josalggui/RFAutoMaTE/figures/Block diagram.png

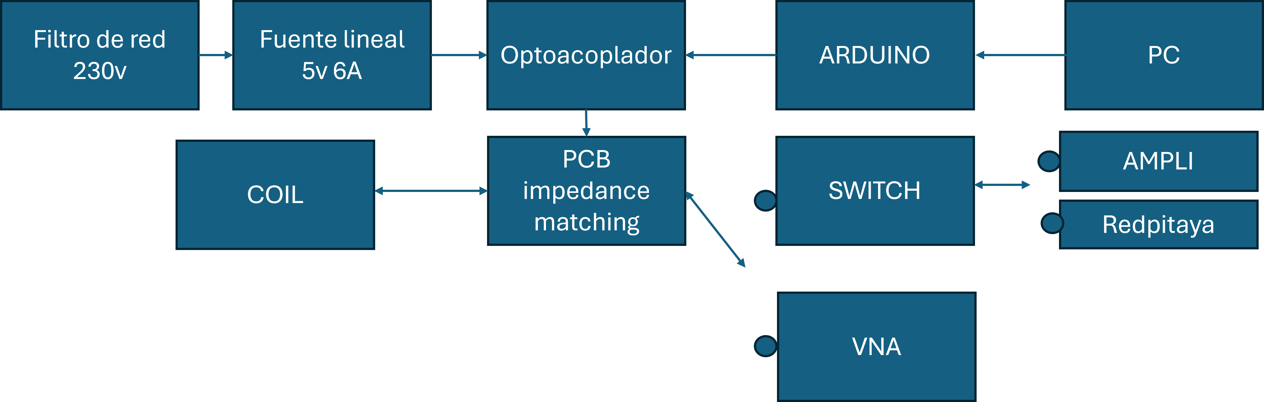
figures/Block diagram.png
