josalggui/RFAutoMaTE/figures/caja 2.jpg

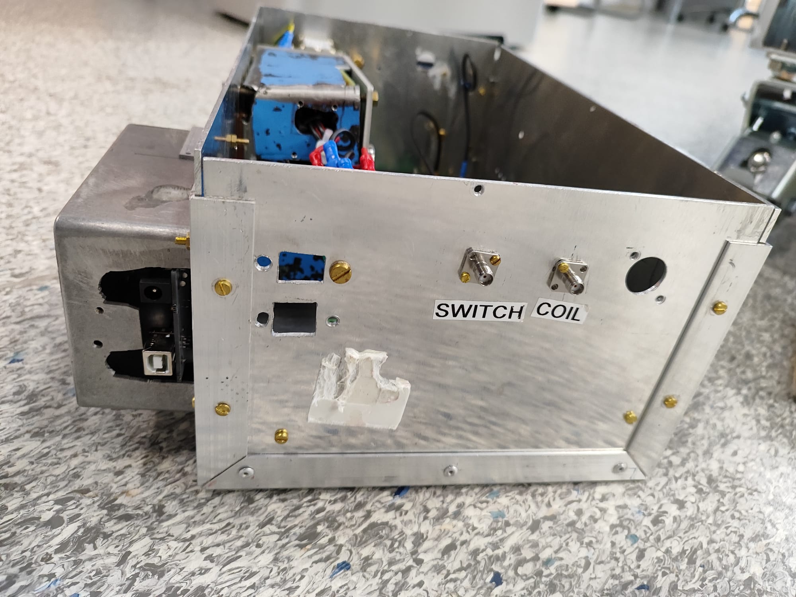
figures/caja 2.jpg
