josalggui/RFAutoMaTE/figures/caja 5.jpg

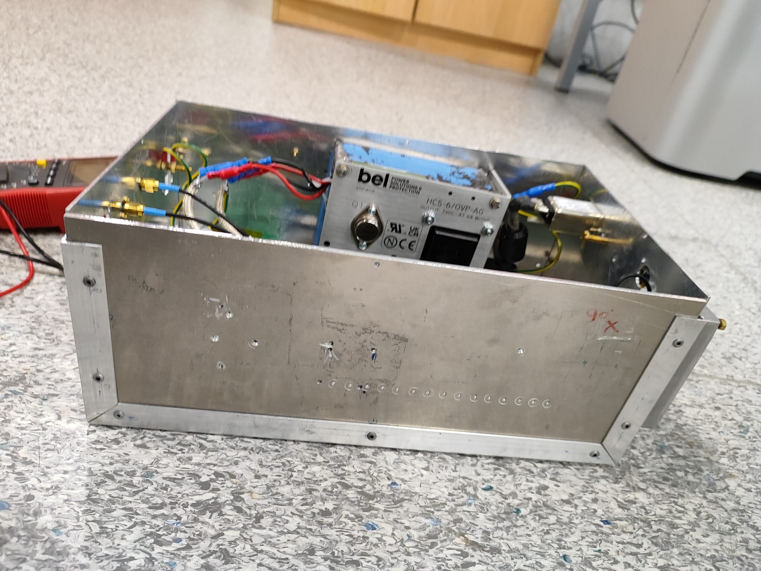
figures/caja 5.jpg
