josalggui/RFAutoMaTE/figures/caja 6.jpg

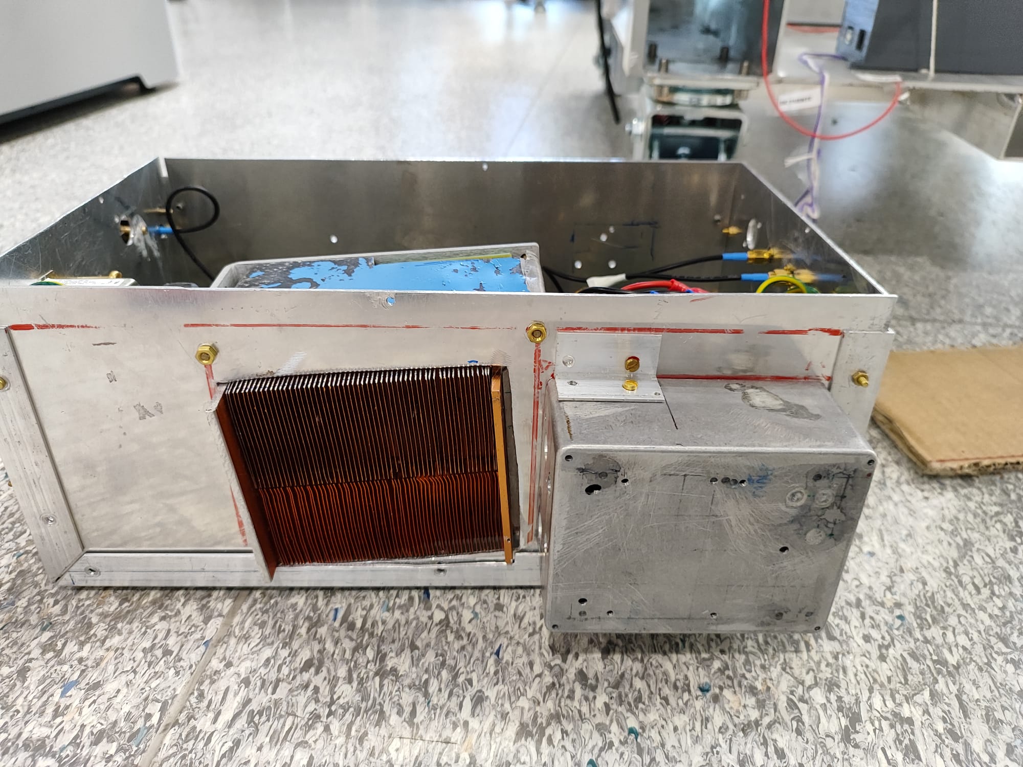
figures/caja 6.jpg
