josalggui/RFAutoMaTE/figures/fuenet lineal 2.jpg

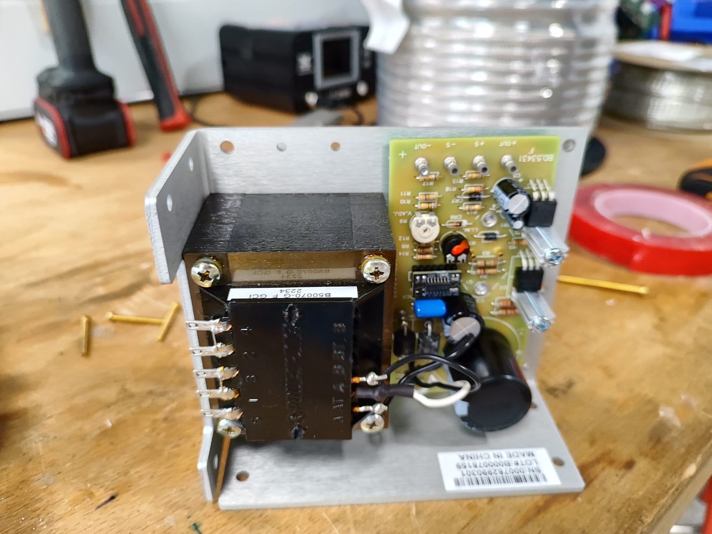
figures/fuenet lineal 2.jpg
