josalggui/RFAutoMaTE/figures/fuenet lineal 3.jpg

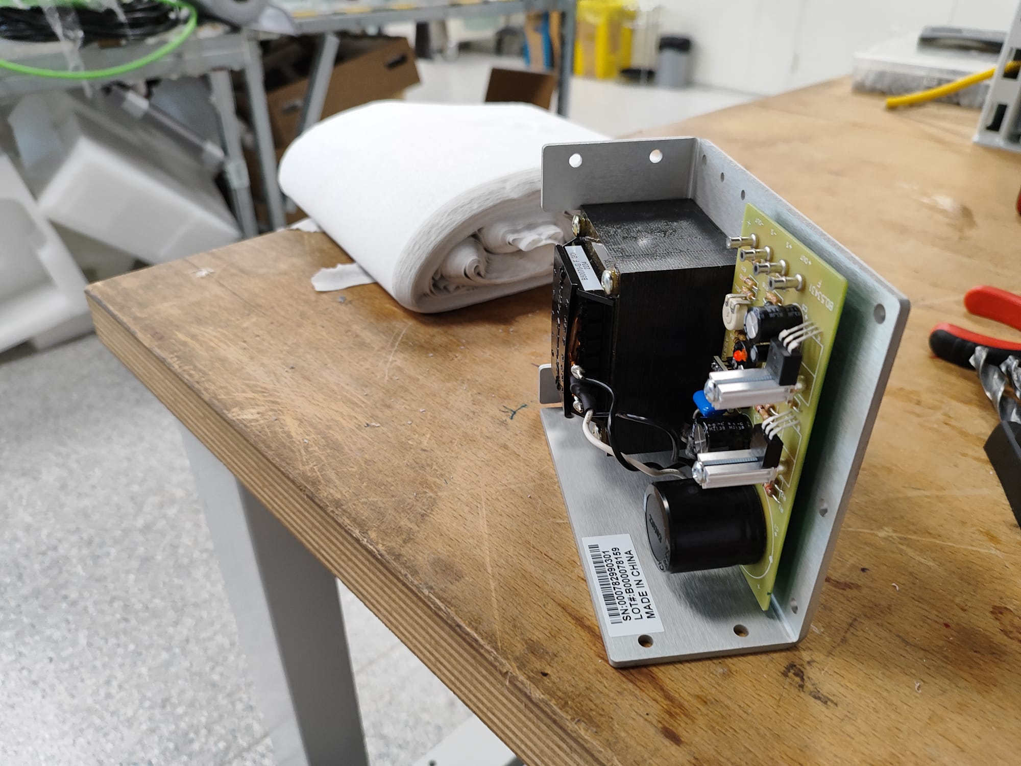
figures/fuenet lineal 3.jpg
