josalggui/RFAutoMaTE/figures/fuenete lineal 4.jpg

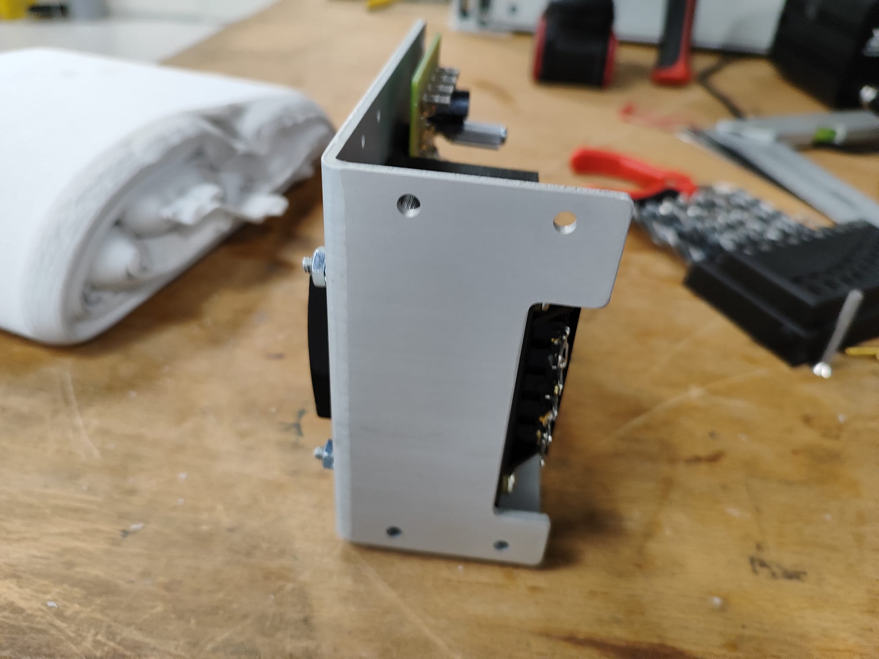
figures/fuenete lineal 4.jpg
