josalggui/RFAutoMaTE/figures/pcb sin montar2.jpg

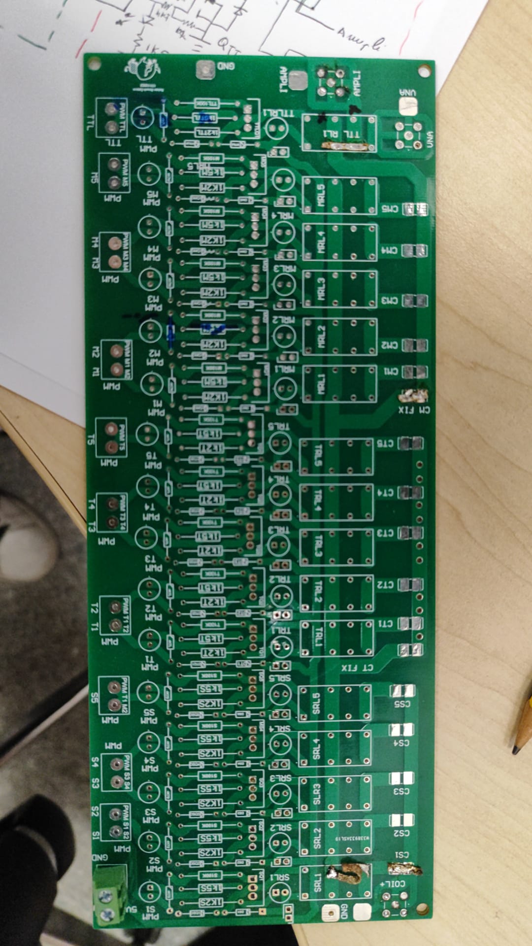
figures/pcb sin montar2.jpg
