josalggui/RFAutoMaTE/figures/pcb sin montar3.jpg

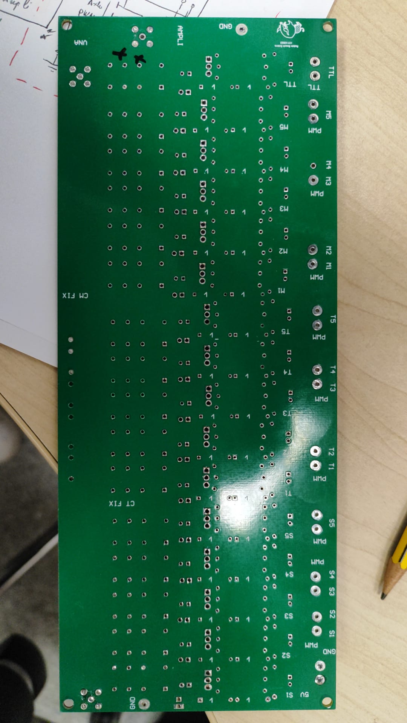
figures/pcb sin montar3.jpg
