josalggui/RFAutoMaTE/optoacoplador/NPN.PNG

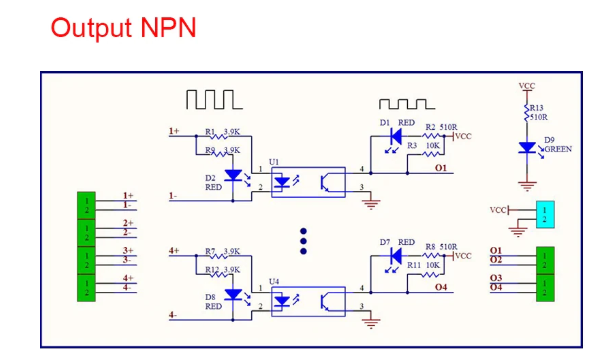
optoacoplador/NPN.PNG
