josalggui/RFAutoMaTE/PCB/Aclaración esquema.jpg

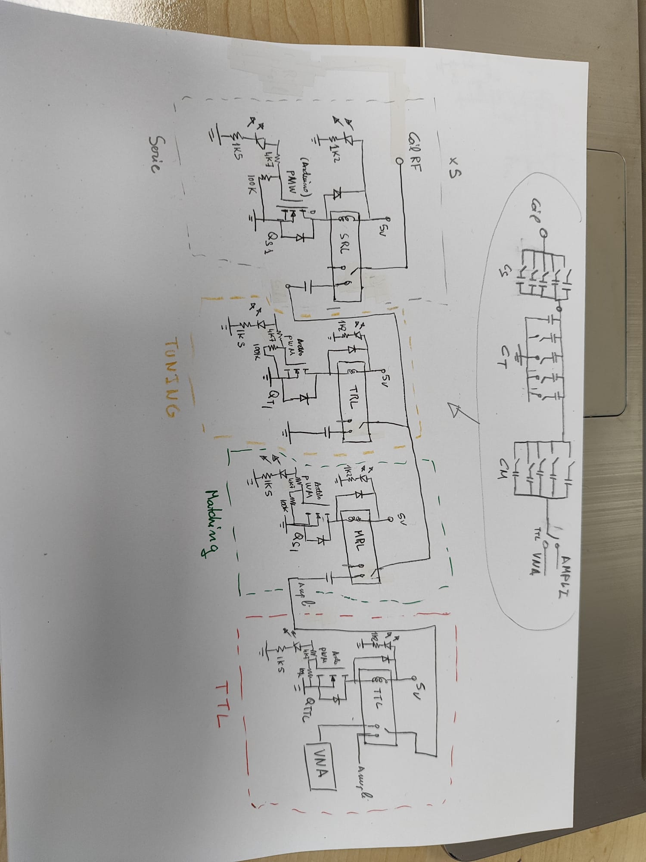
PCB/Aclaración esquema.jpg
